eskeartjom/RT5XP-EXP/Resources/IMG_3277.png

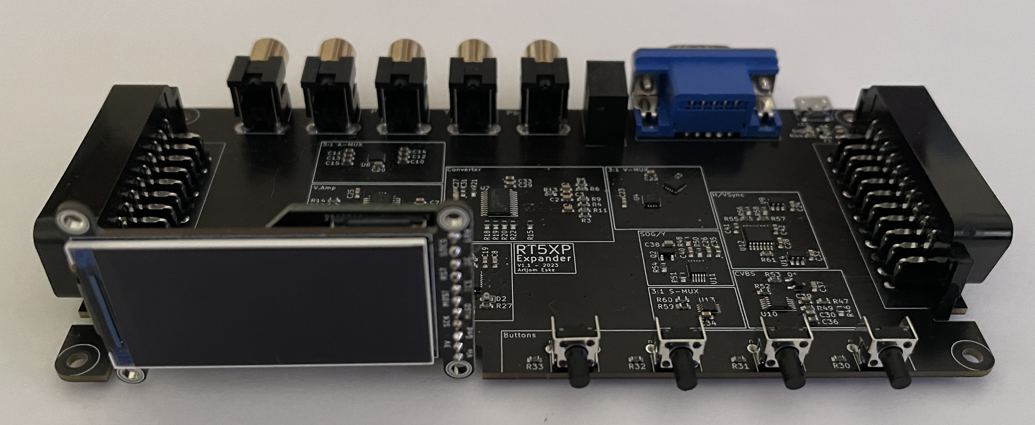
Resources/IMG_3277.png
